mwhome/wortuhr/LedDriver.h

//*****************************************************************************
// LedDriver.h
//*****************************************************************************

#ifndef LEDDRIVER_H
#define LEDDRIVER_H

#include <Adafruit_NeoPixel.h>
#include "Configuration.h"
#include "Colors.h"

typedef struct layout_s {
  uint8_t matrix[NUMPIXELS_Y * NUMPIXELS_X];
  uint8_t corners[NUMPIXELS_CORNERS];
  uint8_t alarm;
  uint8_t ledsPerLetter;
  uint8_t ledsPerCorner;
  uint8_t ledsPerAlarm;
} layout_t;

#ifdef LED_LAYOUT_HORIZONTAL_1
    const layout_t ledMap = {
      {
          0,   1,   2,   3,   4,   5,   6,   7,   8,   9,  10,
         21,  20,  19,  18,  17,  16,  15,  14,  13,  12,  11,
         22,  23,  24,  25,  26,  27,  28,  29,  30,  31,  32,
         43,  42,  41,  40,  39,  38,  37,  36,  35,  34,  33,
         44,  45,  46,  47,  48,  49,  50,  51,  52,  53,  54,
         65,  64,  63,  62,  61,  60,  59,  58,  57,  56,  55,
         66,  67,  68,  69,  70,  71,  72,  73,  74,  75,  76,
         87,  86,  85,  84,  83,  82,  81,  80,  79,  78,  77,
         88,  89,  90,  91,  92,  93,  94,  95,  96,  97,  98,
        109, 108, 107, 106, 105, 104, 103, 102, 101, 100,  99
      },
      {111, 112, 113, 110}, 
      114,
      1,
      1,
      1
    };
#endif

#ifdef LED_LAYOUT_HORIZONTAL_2
    const layout_t ledMap = {
      {
         103, 104, 105, 106, 107, 108, 109, 110, 111, 112, 113, 
         102, 101, 100, 99,  98,  97,  96,  95,  94,  93,  92,
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
          9,  13,  30,  33,  50,  53,  71,  74,  91,  94, 112,
         10,  12,  31,  32,  51,  52,  72,  73,  92,  93, 113
      },
      {0, 103, 114,  11},
      62,
      1,
      1,
      1
    };
#endif

class LedDriver {
public:
    LedDriver();
    ~LedDriver();

    void clear();
    void show();
    uint32_t getPixelColor(uint8_t x, uint8_t y);
    uint32_t getPixelColor(uint8_t num);
    void setPixel(uint8_t x, uint8_t y, uint8_t color, uint8_t brightness);
    void setPixel(uint8_t num, uint8_t color, uint8_t brightness);
    void setPixelColor(uint8_t x, uint8_t y, uint32_t color32bit);
    void setPixelColor(uint8_t num, uint32_t color32bit);
    void setPixelRGB(uint8_t x, uint8_t y, uint8_t red, uint8_t green, uint8_t blue);
    void setPixelRGB(uint8_t num, uint8_t red, uint8_t green, uint8_t blue );
    void updateColorWheel();

private:
    Adafruit_NeoPixel* strip;
    uint8_t m_wheelPos;
    uint32_t m_wheelColor;
    uint8_t ledMapCalc[NUMPIXELS_Y * NUMPIXELS_X + NUMPIXELS_CORNERS + 1];
    uint32_t wheel(uint8_t wheelPos);
    uint8_t getLedsCount();
    void calculateLedMap();
};

#endif
